skuep/Mobile-Whip/ltspice/battery-protection.asc

D1: zener; UFZV6_2B
M1: pmos; SI3445DV
M2: pmos; SI3445DV
R1: res; 5.1K
R2: res; 100K
R3: res; 100K
R4: res; 40
R5: res; 1K
R6: res; 1K
R7: res; 220K
U1: TLV431
V1: voltage; PWL(0 4.2 100m 4.2 200m 0 300m -4.2 400m -4.2 500m 0 600m 4.2); Rser=.1 Cpar=1p
Named nets: 0
.tran 0 1 0 1m
.inc TLV431.lib
